jeffreyer/Eink/include/app_control.h

#pragma once

#include <stdint.h>

#ifdef __cplusplus
extern "C" {
#endif

void app_set_page(int32_t page, int32_t subpage);
void app_set_subpage(int32_t subpage);
int32_t app_get_page_count(void);
int32_t app_get_page_index(void);
int32_t app_get_subpage_index(void);
bool app_set_module_enabled(int32_t page, bool enabled);

#ifdef __cplusplus
}
#endif
