jeffreyer/Eink/include/eink6.h

#pragma once
#include <Arduino.h>

// Color byte values are copied from the original MSP430 reference code.
enum EpdColorByte : uint8_t {
    COLOR_BLACK = 0x00,
    COLOR_WHITE = 0x11,
    COLOR_YELLOW = 0x22,
    COLOR_RED = 0x33,
    COLOR_BLUE = 0x55,
    COLOR_GREEN = 0x66,
};

// 画布绘制用的 4bit 颜色值（每个像素 4bit，2 像素/字节）。
// 与 GUI_Paint Scale=7 模式配合使用，最终写入帧缓冲时左移 4 位即得 EpdColorByte。
enum EpdColorNibble : uint8_t {
    NIBBLE_BLACK  = 0x0,
    NIBBLE_WHITE  = 0x1,
    NIBBLE_YELLOW = 0x2,
    NIBBLE_RED    = 0x3,
    NIBBLE_BLUE   = 0x5,
    NIBBLE_GREEN  = 0x6,
};

// EPD resolution from original code: 480x720, 4bpp packed (2 pixels per byte).
// Panel is GDEH0154E01: 240x240, 4bpp packed (2 pixels per byte)
static const uint16_t EPD_WIDTH = 240;
static const uint16_t EPD_HEIGHT = 240;
static const uint32_t EPD_FRAME_BYTES = (EPD_WIDTH * EPD_HEIGHT) / 2; // 240*240/2 = 28800

#define ALLSCREEN_BYTES EPD_FRAME_BYTES

// 异步刷屏参数（调度逻辑见 include/epd_async.h）：
// epdDisplayImage 发完 0x12 刷新命令后立即返回（不等待 BUSY/不断电），
// 6 色全刷约 20-30 秒，故 30 秒后唤醒补断电；未休眠时由主循环兜底断电
#define EPD_ASYNC_REFRESH_SLEEP_S 28
#define EPD_PANEL_POWEROFF_DELAY_MS 3000
#define EPD_ASYNC_WAIT_TIMEOUT_MS 5000

bool epdPanelIsIdle(void);
void epdPanelPowerOff(void);
int epdPanelBusyRaw(void);
void epdPanelHoldPins(bool hold);

int init_eink6();
int gui_drawtext(const char* str);
void epdDisplaySolid(EpdColorByte color);
void epdDisplayImage(const unsigned char* imgData, uint32_t dataLen);
void epdEnterDeepSleep();
void epdReset();
void epdTryFixBusyPolarity();
void epdInitJD7601();
void epdInitJD7601WaterRipple_v2();
bool epdWaitBusy(uint32_t timeoutMs);
bool epdWaitBusyStage(const char* stage, uint32_t timeoutMs);
void epdWriteCommand(uint8_t cmd);
void epdWriteData(uint8_t data);
