jeffreyer/Eink/include/GUI_Paint.h

#ifndef GUI_PAINT_H
#define GUI_PAINT_H

#include "fonts.h"
#include <stdint.h>
/**
 * Image attributes
**/



#define UBYTE   uint8_t
#define UWORD   uint16_t
#define UDOUBLE uint32_t

/**
 * Image attributes
**/
typedef struct {
    UBYTE *Image;
    UWORD Width;
    UWORD Height;
    UWORD WidthMemory;
    UWORD HeightMemory;
    UWORD Color;
    UWORD Rotate;
    UWORD Mirror;
    UWORD WidthByte;
    UWORD HeightByte;
    UWORD Scale;
} PAINT;
extern PAINT Paint;

/**
 * Display rotate
**/
#define ROTATE_0            0
#define ROTATE_90           90
#define ROTATE_180          180
#define ROTATE_270          270

/**
 * Display Flip
**/
typedef enum {
    MIRROR_NONE  = 0x00,
    MIRROR_HORIZONTAL = 0x01,
    MIRROR_VERTICAL = 0x02,
    MIRROR_ORIGIN = 0x03,
} MIRROR_IMAGE;
#define MIRROR_IMAGE_DFT MIRROR_NONE

/**
 * image color
**/

#define WHITE     0xFF
#define BLACK     0x00
#define RED       0x00
// Color
#define  BLACK0   0x03
#define  WHITE0   0x00
#define  YELLOW0  0x01
#define  RED0     0x02

/*
#define IMAGE_BACKGROUND    WHITE
#define FONT_FOREGROUND     BLACK
#define FONT_BACKGROUND     WHITE
*/
#define TRUE 1
#define FALSE 0

//4 Gray level
#define  GRAY1 0x03 //Blackest
#define  GRAY2 0x02
#define  GRAY3 0x01 //gray
#define  GRAY4 0x00 //white

// 黑白屏（Scale=2）的中间灰：Paint_SetPixel 用 4x4 Bayer 有序抖动表达，
// 让原本的黄色等浅色在黑白屏上仍可辨识（不会直接消失成白底）
#define  GRAY_LIGHT 0xC0  // 约 75% 白
#define  GRAY_MID   0x80  // 约 50% 白
#define  GRAY_DARK  0x40  // 约 25% 白

/**
 * The size of the point
**/
typedef enum {
    DOT_PIXEL_1X1  = 1,		// 1 x 1
    DOT_PIXEL_2X2  , 		// 2 X 2
    DOT_PIXEL_3X3  ,		// 3 X 3
    DOT_PIXEL_4X4  ,		// 4 X 4
    DOT_PIXEL_5X5  , 		// 5 X 5
    DOT_PIXEL_6X6  , 		// 6 X 6
    DOT_PIXEL_7X7  , 		// 7 X 7
    DOT_PIXEL_8X8  , 		// 8 X 8
} DOT_PIXEL;
#define DOT_PIXEL_DFT  DOT_PIXEL_1X1  //Default dot pilex

/**
 * Point size fill style
**/
typedef enum {
    DOT_FILL_AROUND  = 1,		// dot pixel 1 x 1
    DOT_FILL_RIGHTUP  , 		// dot pixel 2 X 2
} DOT_STYLE;
#define DOT_STYLE_DFT  DOT_FILL_AROUND  //Default dot pilex

/**
 * Line style, solid or dashed
**/
typedef enum {
    LINE_STYLE_SOLID = 0,
    LINE_STYLE_DOTTED,
} LINE_STYLE;

/**
 * Whether the graphic is filled
**/
typedef enum {
    DRAW_FILL_EMPTY = 0,
    DRAW_FILL_FULL,
} DRAW_FILL;

/**
 * Custom structure of a time attribute
**/
typedef struct {
    UWORD Year;  //0000
    UBYTE  Month; //1 - 12
    UBYTE  Day;   //1 - 30
    UBYTE  Hour;  //0 - 23
    UBYTE  Min;   //0 - 59
    UBYTE  Sec;   //0 - 59
} PAINT_TIME;
extern PAINT_TIME sPaint_time;

//init and Clear
void Paint_NewImage(UBYTE *image, UWORD Width, UWORD Height, UWORD Rotate, UWORD Color);
void Paint_SelectImage(UBYTE *image);
void Paint_SetRotate(UWORD Rotate);
void Paint_SetMirroring(UBYTE mirror);
void Paint_SetPixel(UWORD Xpoint, UWORD Ypoint, UWORD Color);
void Paint_SetScale(UBYTE scale);

void Paint_Clear(UWORD Color);
void Paint_ClearWindows(UWORD Xstart, UWORD Ystart, UWORD Xend, UWORD Yend, UWORD Color);

//Drawing
void Paint_DrawPoint(UWORD Xpoint, UWORD Ypoint, UWORD Color, DOT_PIXEL Dot_Pixel, DOT_STYLE Dot_FillWay);
void Paint_DrawLine(UWORD Xstart, UWORD Ystart, UWORD Xend, UWORD Yend, UWORD Color, LINE_STYLE Line_Style, DOT_PIXEL Dot_Pixel);
void Paint_DrawRectangle(UWORD Xstart, UWORD Ystart, UWORD Xend, UWORD Yend, UWORD Color, DRAW_FILL Draw_Fill, DOT_PIXEL Dot_Pixel);
void Paint_DrawCircle(UWORD X_Center, UWORD Y_Center, UWORD Radius, UWORD Color, DRAW_FILL Draw_Fill, DOT_PIXEL Dot_Pixel);

//Display string
void Paint_DrawChar(UWORD Xstart, UWORD Ystart, const char Acsii_Char, sFONT* Font, UWORD Color_Foreground, UWORD Color_Background);
void Paint_DrawString_EN(UWORD Xstart, UWORD Ystart, const char * pString, sFONT* Font, UWORD Color_Foreground, UWORD Color_Background);
void Paint_DrawString_CN(UWORD Xstart, UWORD Ystart, const char * pString, cFONT* font, UWORD Color_Foreground, UWORD Color_Background);
void Paint_DrawNum(UWORD Xpoint, UWORD Ypoint, int32_t Nummber, sFONT* Font, UWORD Color_Foreground, UWORD Color_Background);
void Paint_DrawNumDecimals(UWORD Xpoint, UWORD Ypoint, double Nummber, sFONT* Font, UWORD Digit, UWORD Color_Foreground, UWORD Color_Background); // Able to display decimals
void Paint_DrawTime(UWORD Xstart, UWORD Ystart, PAINT_TIME *pTime, sFONT* Font, UWORD Color_Foreground, UWORD Color_Background);

//pic
void Paint_DrawBitMap(const unsigned char* image_buffer);
void Paint_DrawBitMap_Paste(const unsigned char* image_buffer, UWORD Xstart, UWORD Ystart, UWORD imageWidth, UWORD imageHeight, UBYTE flipColor);
//void Paint_DrawBitMap_Half(const unsigned char* image_buffer, UBYTE Region);
//void Paint_DrawBitMap_OneQuarter(const unsigned char* image_buffer, UBYTE Region);
//void Paint_DrawBitMap_OneEighth(const unsigned char* image_buffer, UBYTE Region);
void Paint_DrawBitMap_Block(const unsigned char* image_buffer, UBYTE Region);
//Color setting
void Paint_Color_Setting(void);
#endif
